PurpleCatGirl/SB-ATS/IMG_5217.JPG

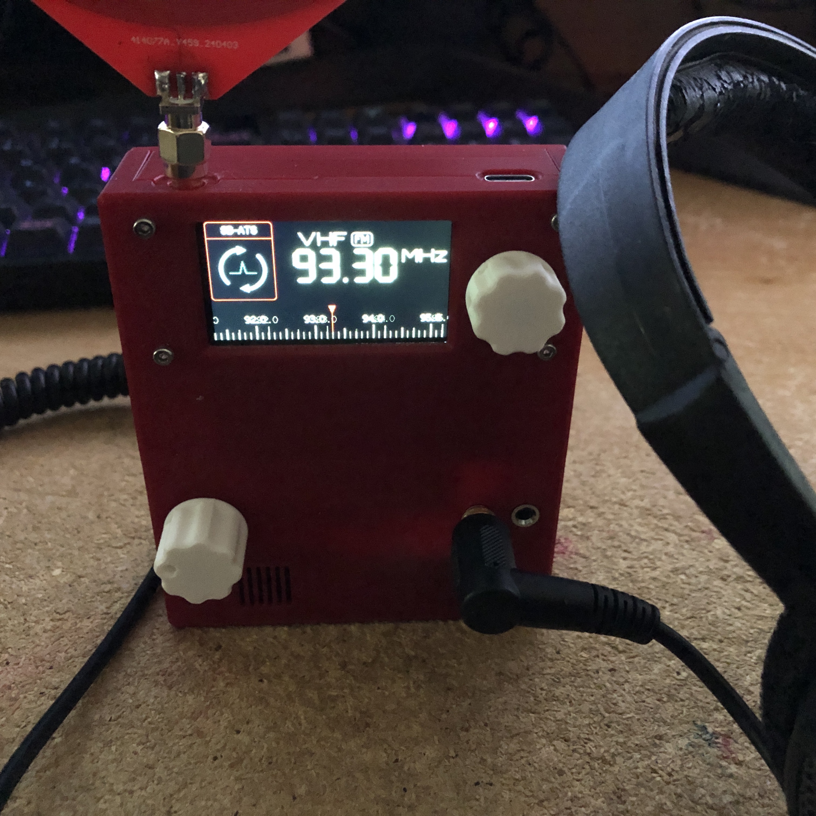
IMG_5217.JPG
